matzapata/dome/dome-device/ConnectionManager.h

#ifndef CONNECTION_MANAGER_H
#define CONNECTION_MANAGER_H

/*************************************************************************************************
 **                                    DEFINES
 *************************************************************************************************/
#define EEPROM_BLOCK_SIZE 50

/*************************************************************************************************
 **                                    GLOBAL VARIABLES
 *************************************************************************************************/
extern char ssid[EEPROM_BLOCK_SIZE];
extern char pass[EEPROM_BLOCK_SIZE];
extern char homeId[EEPROM_BLOCK_SIZE];
extern char deviceId[EEPROM_BLOCK_SIZE];


/*************************************************************************************************
 **                                    FUNCTION PROTOTYPES
 *************************************************************************************************/
void connectionBegin(short configBtn);

#endif
